sanshiki/deskGPT/stm32/deskGPT/Applications/inc/patch_flac.h

#define VS1053B_PATCHLEN  5433  //with FLAC decoder       
 //VS1053B: Patches with FLAC decoder 1.1 (2009-06-23) 
static const unsigned short vs1053b_patch[VS1053B_PATCHLEN] = 
 { 
   0x0007, 0x0001, 0x8300, 0x0006, 0x0202, 0xb080, 0x0024, 0x0007, /*    0 */ 
   0x9257, 0x3f00, 0x0024, 0x0030, 0x0297, 0x3f00, 0x0024, 0x0006, /*    8 */ 
   0x0017, 0x3f10, 0x0024, 0x3f00, 0x0024, 0x0000, 0xf8d7, 0xf400, /*   10 */ 
   0x55c0, 0x0000, 0x0817, 0xf400, 0x57c0, 0x0000, 0x004d, 0x000a, /*   18 */ 
   0x708f, 0x0000, 0xc44e, 0x280f, 0xe100, 0x0006, 0x2016, 0x0000, /*   20 */ 
   0x028d, 0x0014, 0x1b01, 0x2800, 0xc795, 0x0015, 0x59c0, 0x0000, /*   28 */ 
   0xfa0d, 0x0039, 0x324f, 0x0000, 0xd40e, 0x2920, 0x41c0, 0x0000, /*   30 */ 
   0x0024, 0x000a, 0x708f, 0x0000, 0xc44e, 0x280a, 0xcac0, 0x0000, /*   38 */ 
   0x028d, 0x6fc2, 0x0024, 0x0019, 0x9301, 0x2800, 0xcbd5, 0x0018, /*   40 */ 
   0x50c0, 0x000c, 0x0981, 0x0000, 0x18c2, 0x290c, 0x4840, 0x3613, /*   48 */ 
   0x0024, 0x290c, 0x4840, 0x4086, 0x184c, 0x6234, 0x0024, 0x0000, /*   50 */ 
   0x0024, 0x2800, 0xcb55, 0x0030, 0x0317, 0x3f00, 0x0024, 0x280a, /*   58 */ 
   0x71c0, 0x002c, 0x9d40, 0x6fc2, 0x0024, 0x0000, 0x0024, 0x2800, /*   60 */ 
   0xcb55, 0x0000, 0x0024, 0x2800, 0x9c40, 0x000a, 0xcac8, 0x3613, /*   68 */ 
   0x0024, 0x3e10, 0xb803, 0x3e14, 0x3811, 0x3e11, 0x3805, 0x3e00, /*   70 */ 
   0x3801, 0x0007, 0xc390, 0x0006, 0xa011, 0x3010, 0x0444, 0x3050, /*   78 */ 
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
   0x0024, 0x3000, 0x0001, 0x3101, 0x8407, 0x6cfe, 0x0024, 0xac42, /* 1128 */ 
   0x0024, 0xaf4e, 0x2040, 0x3911, 0x8024, 0x2802, 0x3940, 0x0000, /* 1130 */ 
   0x0024, 0x0000, 0x0281, 0x2802, 0x30d5, 0x6012, 0x4455, 0x2402, /* 1138 */ 
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
 }; 
