sanshiki/deskGPT/stm32/deskGPT/Core/Src/spi.c

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
/* Includes ------------------------------------------------------------------*/
#include "spi.h"

SPI_HandleTypeDef hspi1;

/* SPI1 init function */
void MX_SPI1_Init(void)
{

  hspi1.Instance = SPI1;
  hspi1.Init.Mode = SPI_MODE_MASTER;
  hspi1.Init.Direction = SPI_DIRECTION_2LINES;
  hspi1.Init.DataSize = SPI_DATASIZE_8BIT;
  hspi1.Init.CLKPolarity = SPI_POLARITY_HIGH;
  hspi1.Init.CLKPhase = SPI_PHASE_2EDGE;
  hspi1.Init.NSS = SPI_NSS_SOFT;
  hspi1.Init.BaudRatePrescaler = SPI_BAUDRATEPRESCALER_256;
  hspi1.Init.FirstBit = SPI_FIRSTBIT_MSB;
  hspi1.Init.TIMode = SPI_TIMODE_DISABLE;
  hspi1.Init.CRCCalculation = SPI_CRCCALCULATION_DISABLE;
  hspi1.Init.CRCPolynomial = 10;
  if (HAL_SPI_Init(&hspi1) != HAL_OK)
  {
    Error_Handler();
  }
}

void HAL_SPI_MspInit(SPI_HandleTypeDef* spiHandle)
{

  GPIO_InitTypeDef GPIO_InitStruct = {0};
  if(spiHandle->Instance==SPI1)
  {
    /* SPI1 clock enable */
    __HAL_RCC_SPI1_CLK_ENABLE();

    __HAL_RCC_GPIOA_CLK_ENABLE();
    /**SPI1 GPIO Configuration
    PA5     ------> SPI1_SCK
    PA6     ------> SPI1_MISO
    PA7     ------> SPI1_MOSI
    */
    GPIO_InitStruct.Pin = SPI1_SCK_Pin|SPI1_SO_Pin|SPI1_SI_Pin;
    GPIO_InitStruct.Mode = GPIO_MODE_AF_PP;
    GPIO_InitStruct.Pull = GPIO_NOPULL;
    GPIO_InitStruct.Speed = GPIO_SPEED_FREQ_VERY_HIGH;
    GPIO_InitStruct.Alternate = GPIO_AF5_SPI1;
    HAL_GPIO_Init(GPIOA, &GPIO_InitStruct);

  }
}

void HAL_SPI_MspDeInit(SPI_HandleTypeDef* spiHandle)
{

  if(spiHandle->Instance==SPI1)
  {
    /* Peripheral clock disable */
    __HAL_RCC_SPI1_CLK_DISABLE();

    /**SPI1 GPIO Configuration
    PA5     ------> SPI1_SCK
    PA6     ------> SPI1_MISO
    PA7     ------> SPI1_MOSI
    */
    HAL_GPIO_DeInit(GPIOA, SPI1_SCK_Pin|SPI1_SO_Pin|SPI1_SI_Pin);

  }
}

/* USER CODE BEGIN 1 */
/**
 * @brief       SPI1速度设置函数
 *   @note      SPI1时钟选择来自APB1, 即PCLK1, �? 42MHz
 *              SPI速度 = PCLK1 / 2^(speed + 1)
 * @param       speed   : SPI1时钟分频系数
                        取�?�为SPI_BAUDRATEPRESCALER_2~SPI_BAUDRATEPRESCALER_2 256
 * @retval      �?
 */
void spi1_set_speed(uint8_t speed)
{
    assert_param(IS_SPI_BAUDRATE_PRESCALER(speed)); /* 判断有效�? */
    __HAL_SPI_DISABLE(&hspi1);             /* 关闭SPI */
    hspi1.Instance->CR1 &= 0XFFC7;         /* �?3-5清零，用来设置波特率 */
    hspi1.Instance->CR1 |= speed << 3;     /* 设置SPI速度 */
    __HAL_SPI_ENABLE(&hspi1);              /* 使能SPI */
}
/* USER CODE END 1 */
