sanshiki/deskGPT/serialv3/iat_tts_test.py

APPID = '6267d3f7'
APISecret = 'ZDRlMDQwMmZjNGJiOTBhYTc5ZWIxY2Ex'
APIKey = '29cd024f42b3faa5e6c15303cf304bc1'
AudioFile = r'./audioFile/pcmFile/filtered_output.pcm'


from moudule import iat

iat.iatRun(AudioFile)
